jeffThompson/EveryRadioStation/Documentation/ERS_01-web.jpg

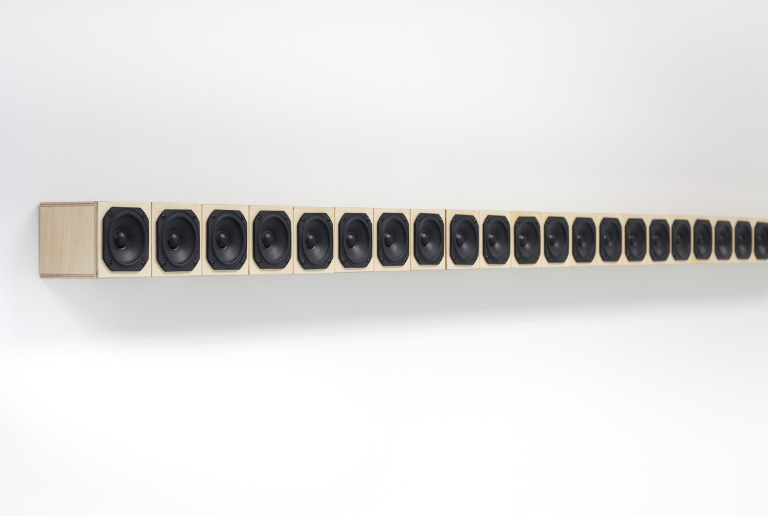
Documentation/ERS_01-web.jpg
