jeffThompson/EveryRadioStation/Documentation/ERS_02-web.jpg

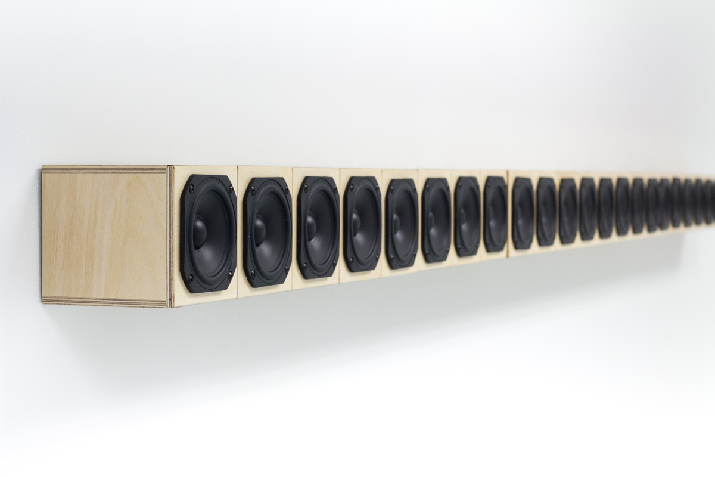
Documentation/ERS_02-web.jpg
