jeffThompson/EveryRadioStation/EarlyVersions/FMRadioLayout_v2.png

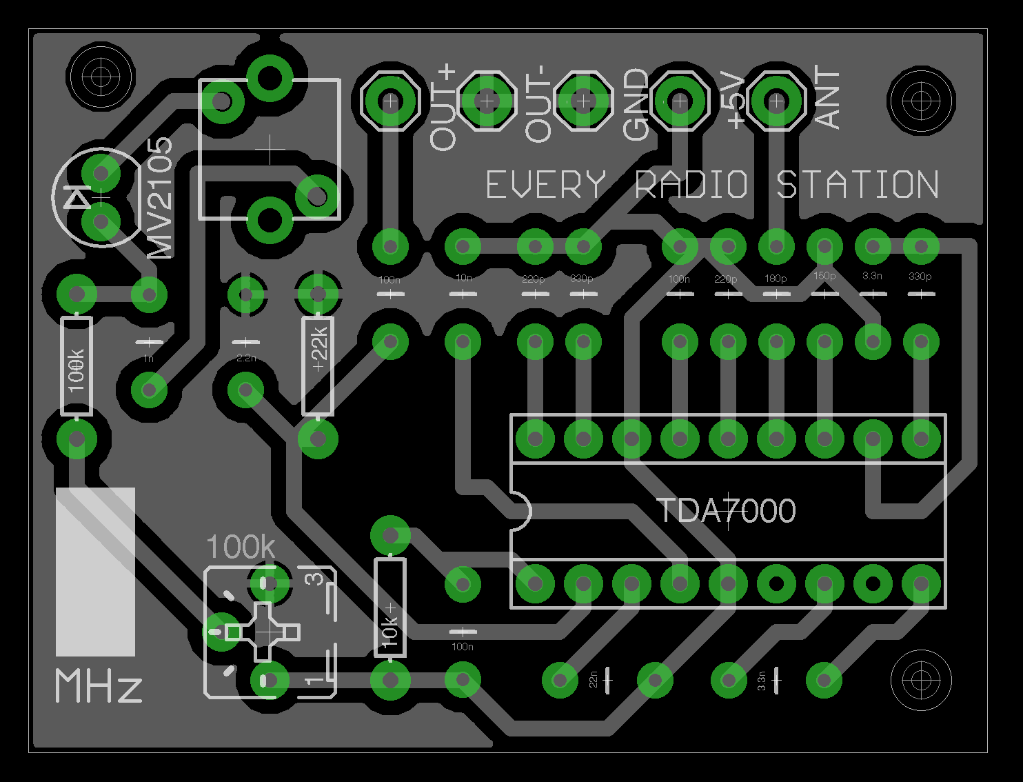
EarlyVersions/FMRadioLayout_v2.png
