jeffThompson/EveryRadioStation/EarlyVersions/FMRadioPCB_v2-4x.png

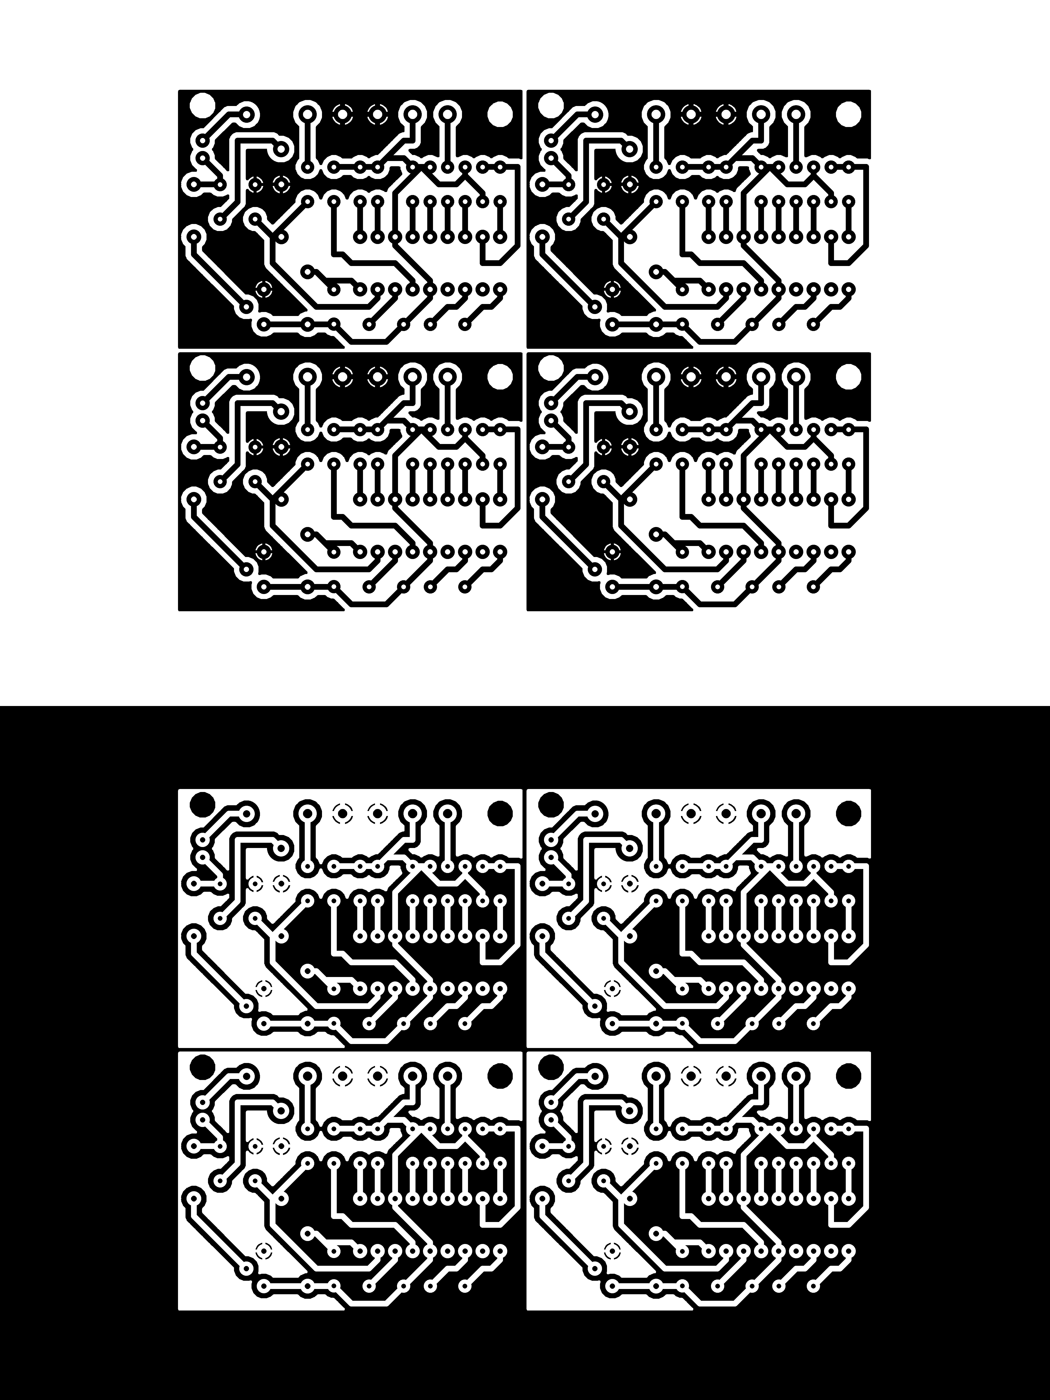
EarlyVersions/FMRadioPCB_v2-4x.png
