jeffThompson/EveryRadioStation/EarlyVersions/FMRadioPCB_v2.png

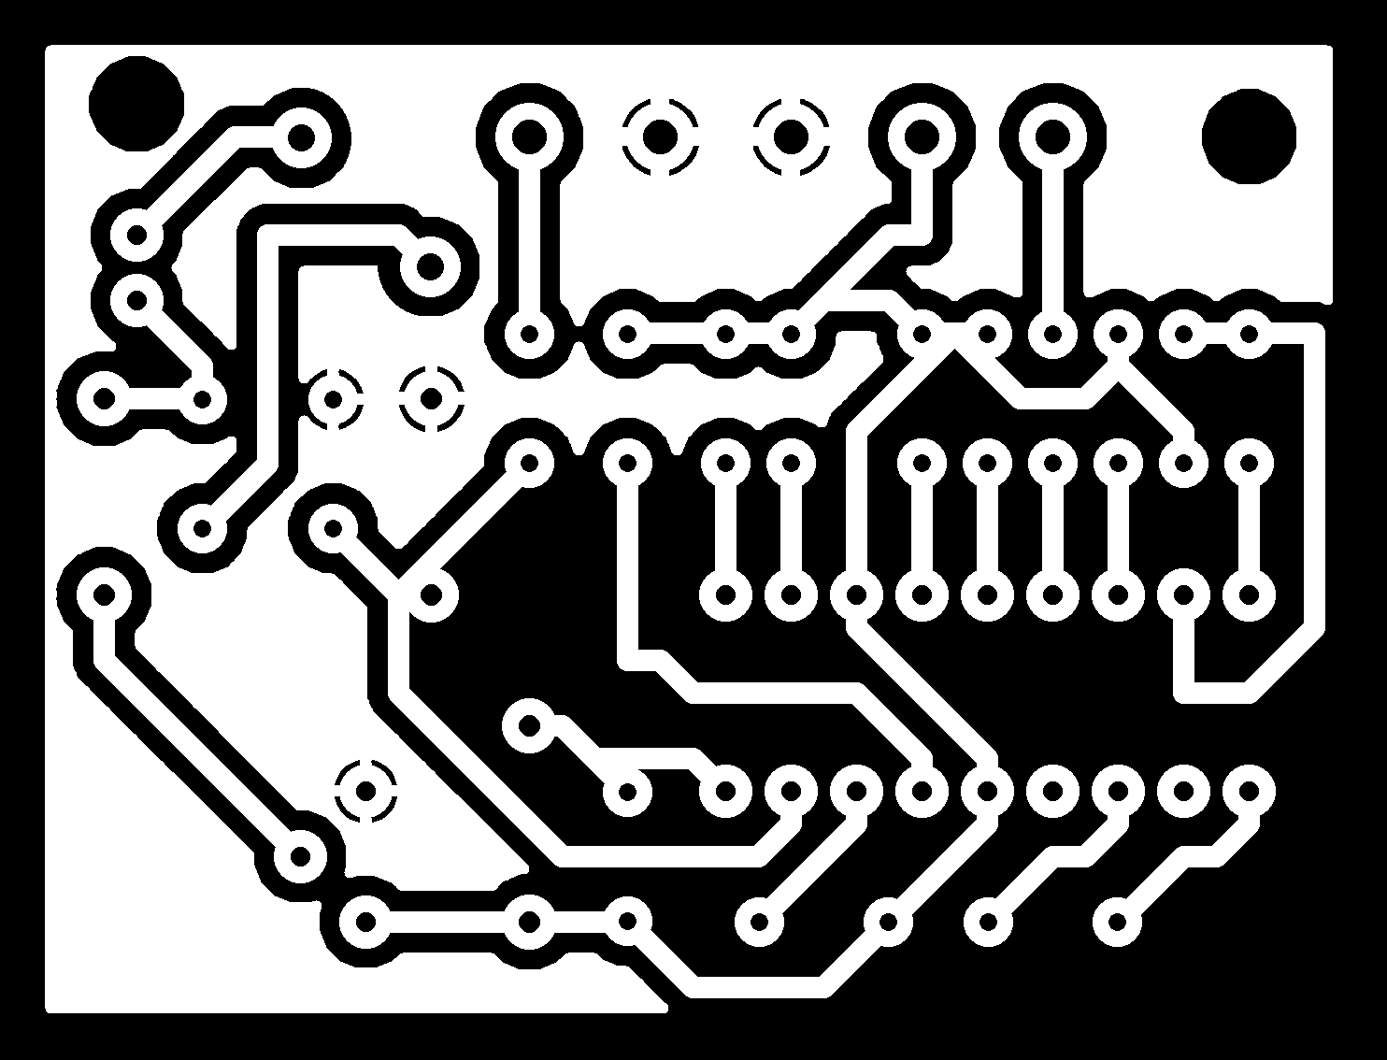
EarlyVersions/FMRadioPCB_v2.png
