jeffThompson/EveryRadioStation/EarlyVersions/Version1/FMRadioLayout-v1.png

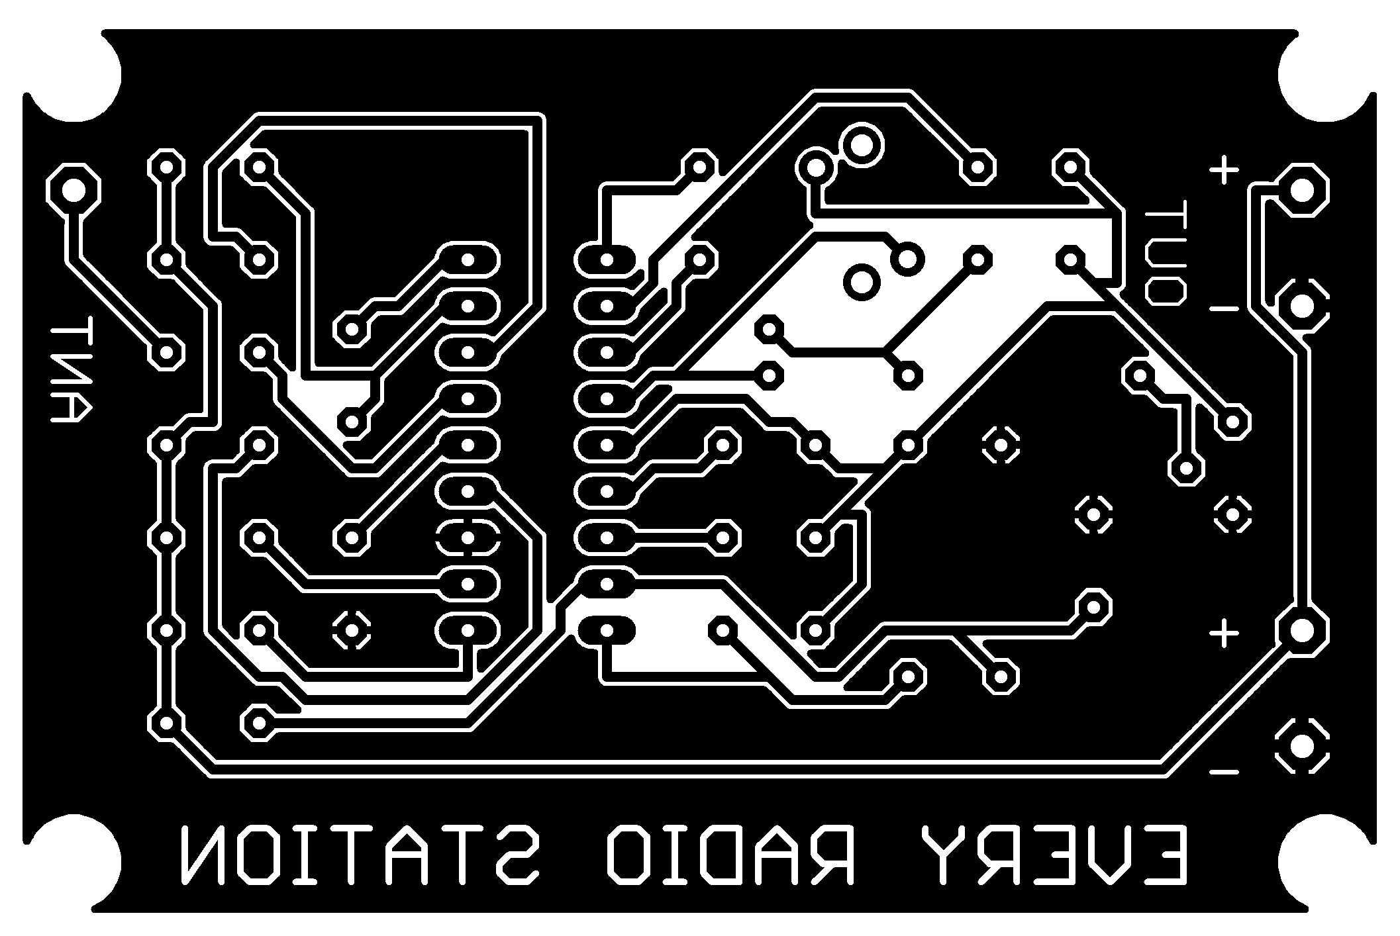
EarlyVersions/Version1/FMRadioLayout-v1.png
