jeffThompson/EveryRadioStation/EarlyVersions/Version1/FMRadioPCB-v1-2x.png

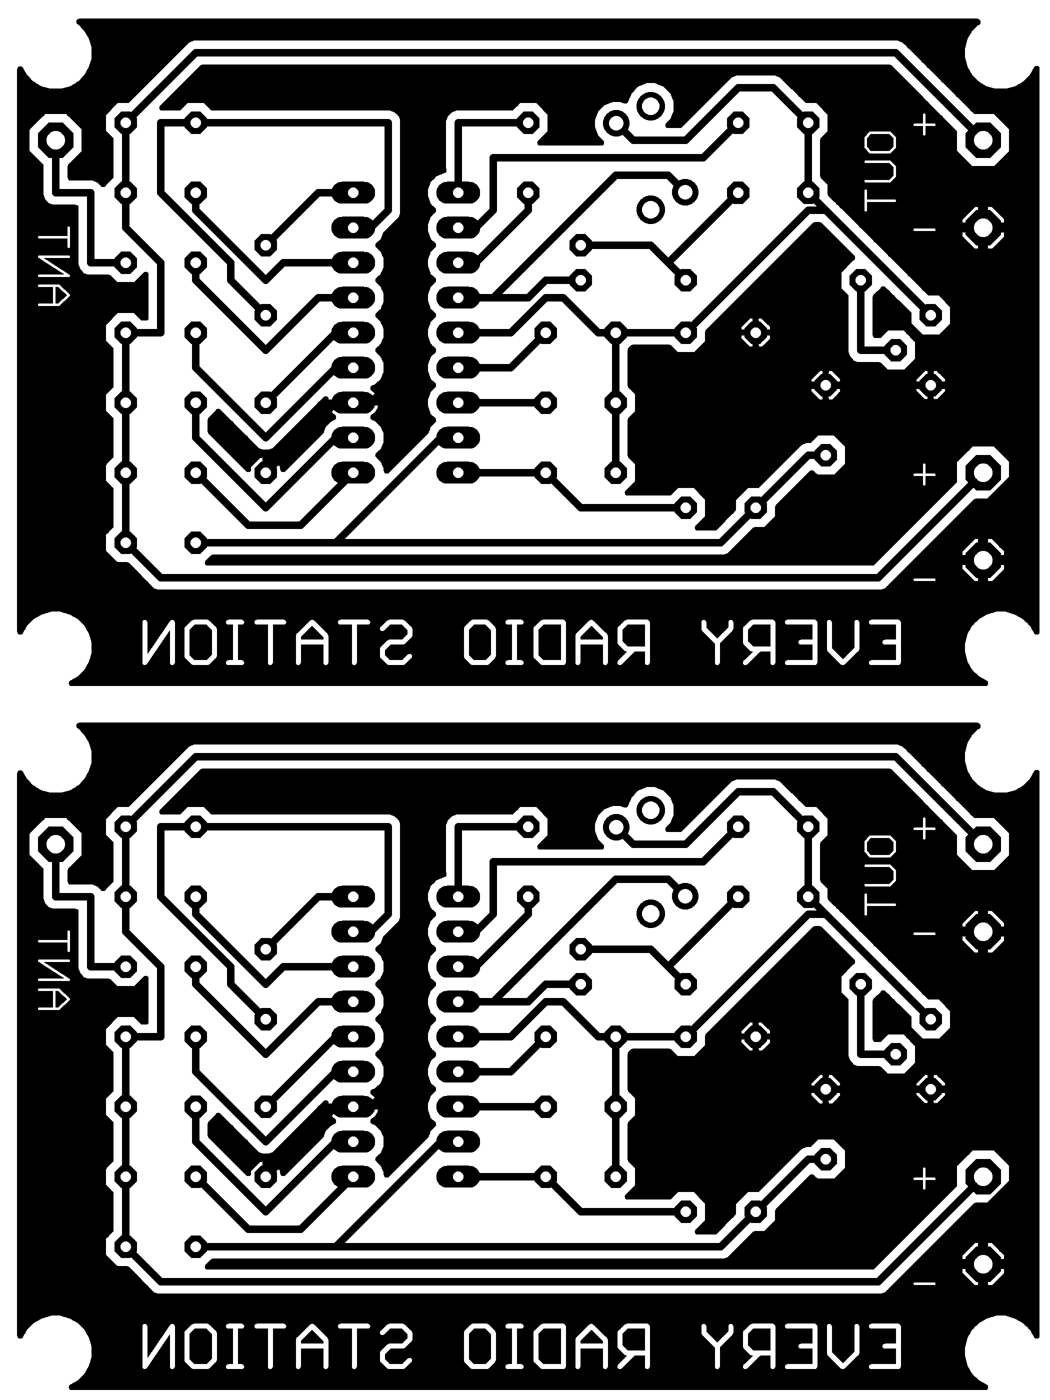
EarlyVersions/Version1/FMRadioPCB-v1-2x.png
