jeffThompson/EveryRadioStation/EarlyVersions/Version1/FMRadioPCB-v1.png

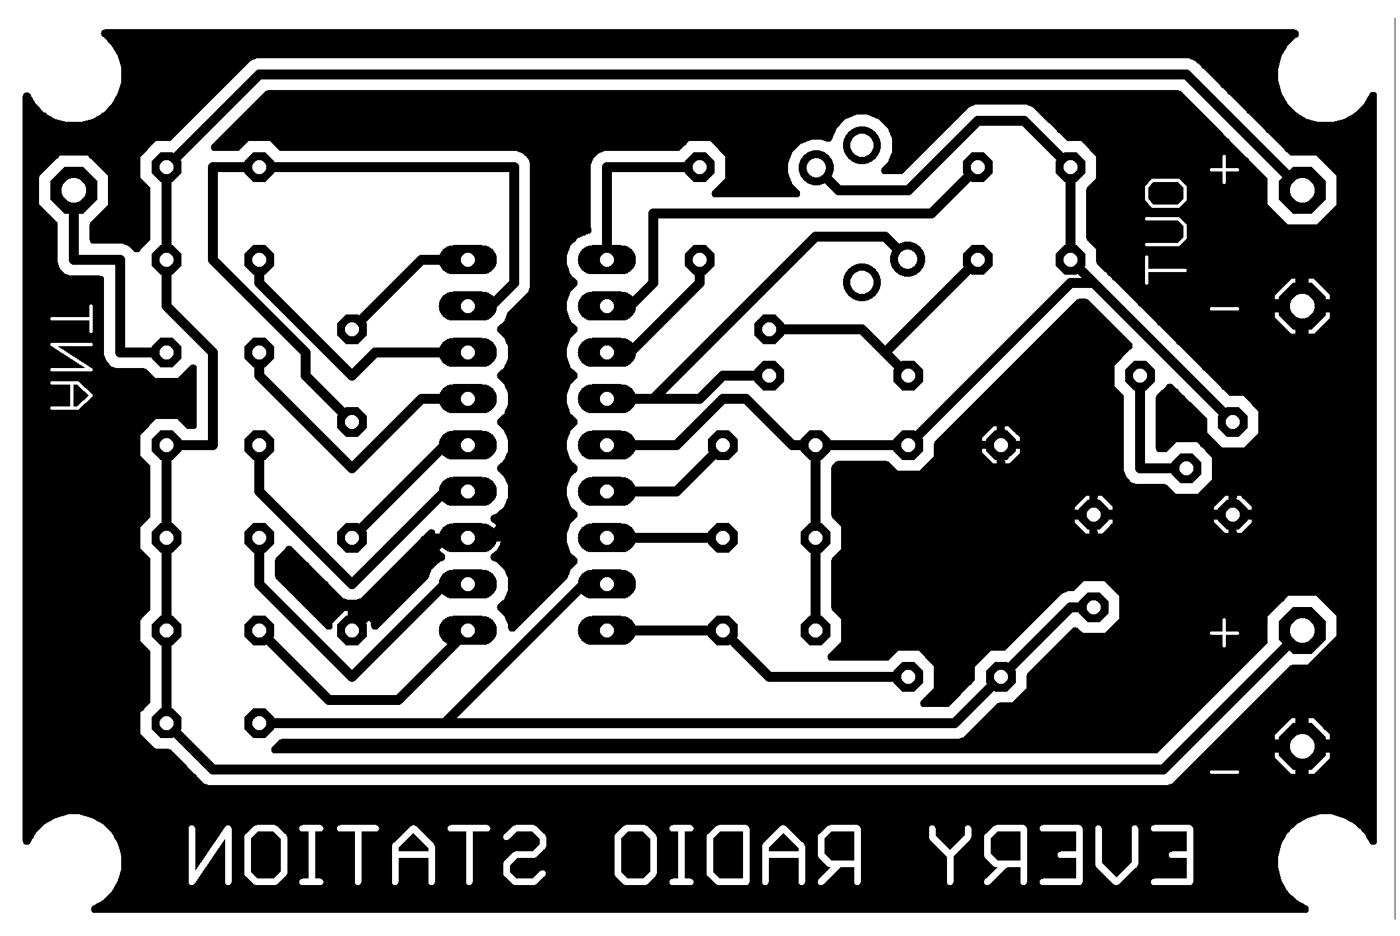
EarlyVersions/Version1/FMRadioPCB-v1.png
