jeffThompson/EveryRadioStation/EarlyVersions/Version1/FMRadioPCB_v2-4x.png

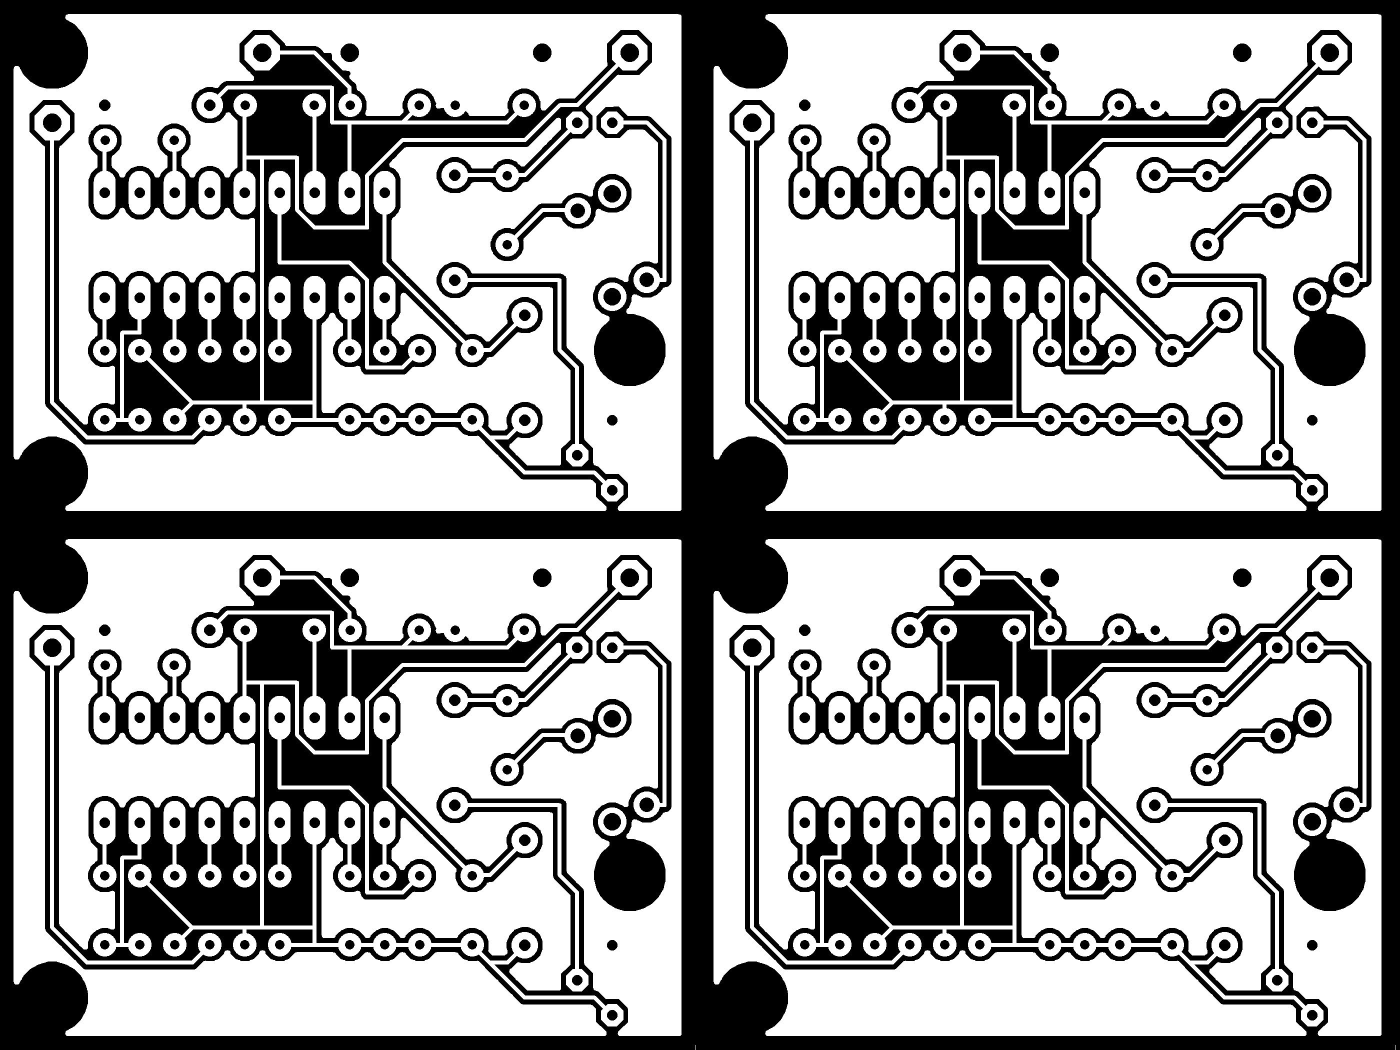
EarlyVersions/Version1/FMRadioPCB_v2-4x.png
