jeffThompson/EveryRadioStation/Renderings/Mockup2-web.jpg

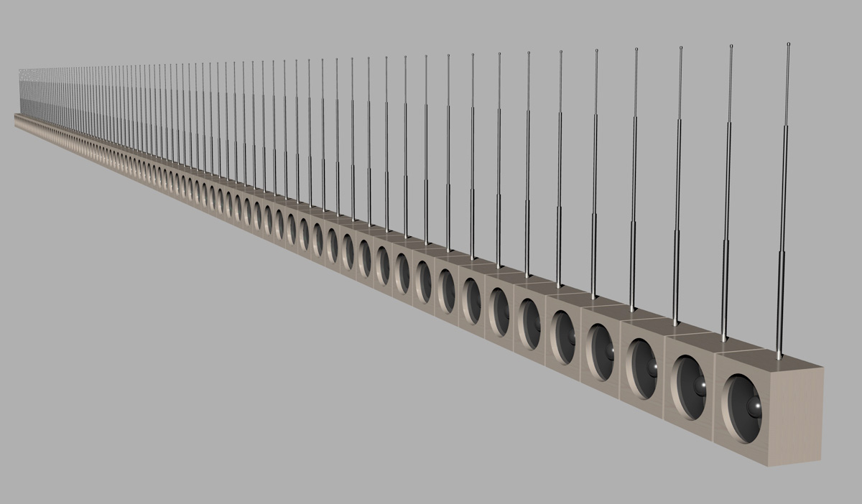
Renderings/Mockup2-web.jpg
