jeffThompson/EveryRadioStation/Renderings/Mockup6.jpg

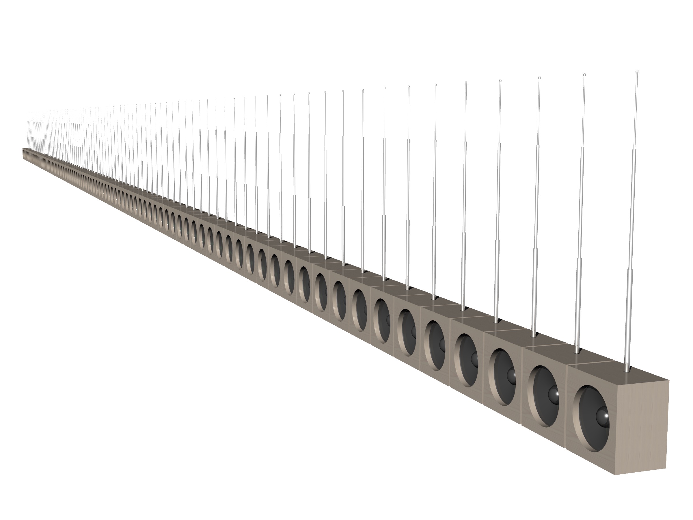
Renderings/Mockup6.jpg
