jeffThompson/EveryRadioStation/Renderings/Mockup7.jpg

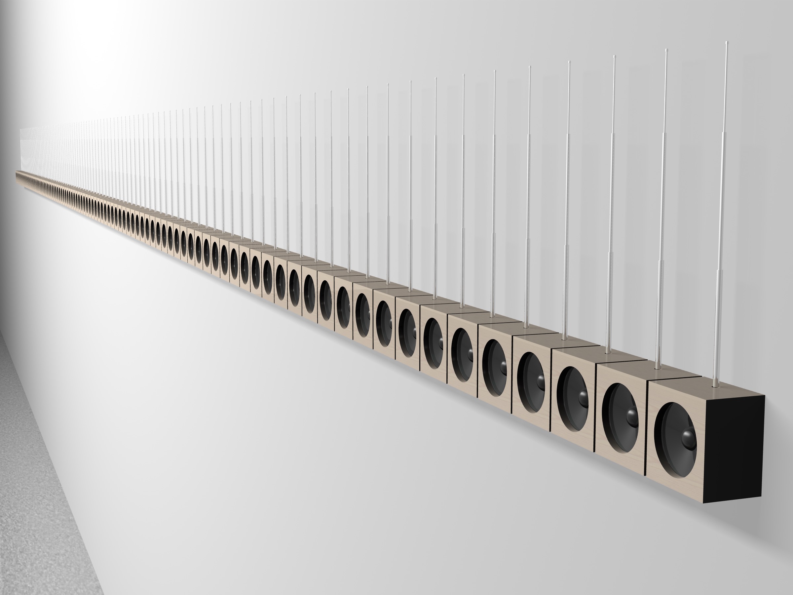
Renderings/Mockup7.jpg
