jeffThompson/EveryRadioStation/Renderings/Mockup8.jpg

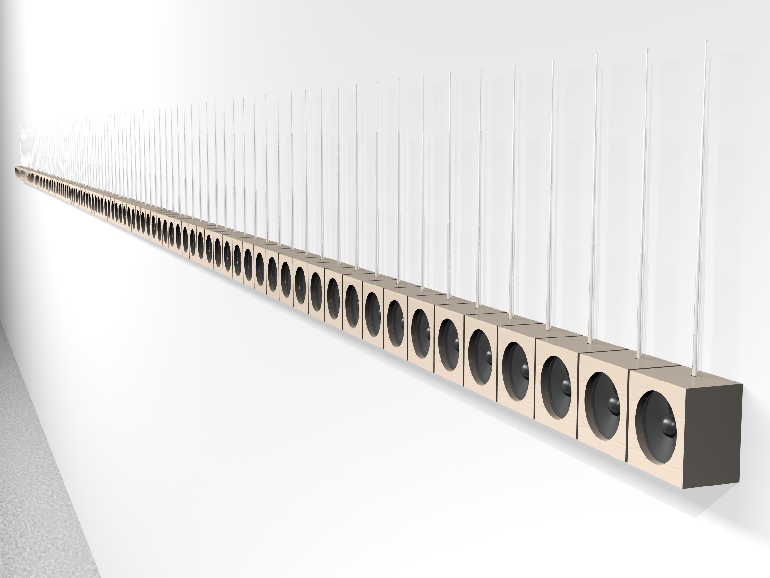
Renderings/Mockup8.jpg
