jeffThompson/EveryRadioStation/Renderings/Mockup9.jpg

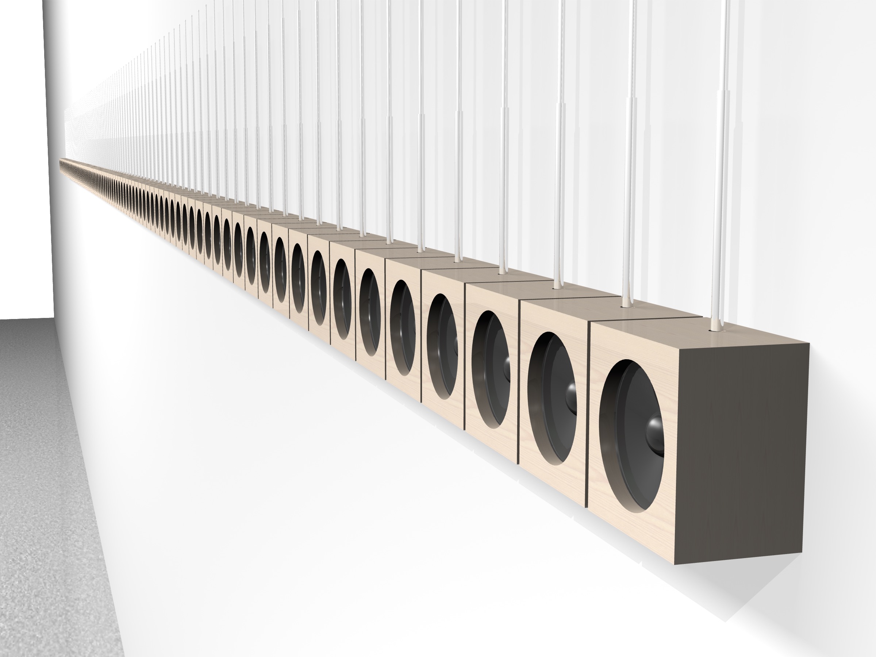
Renderings/Mockup9.jpg
